UC3Music/uC3Moy/Media/Photo/Photo 2.jpg

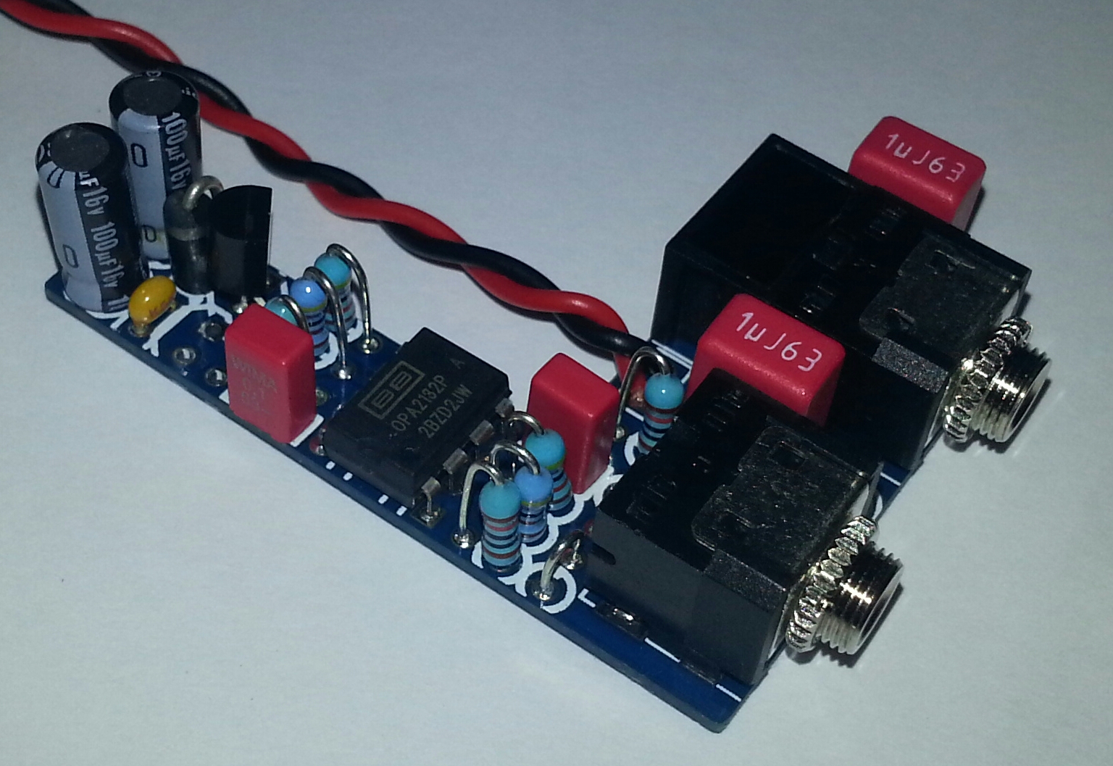
Media/Photo/Photo 2.jpg
