UC3Music/uC3Moy/Media/Photo/Photo 3.jpg

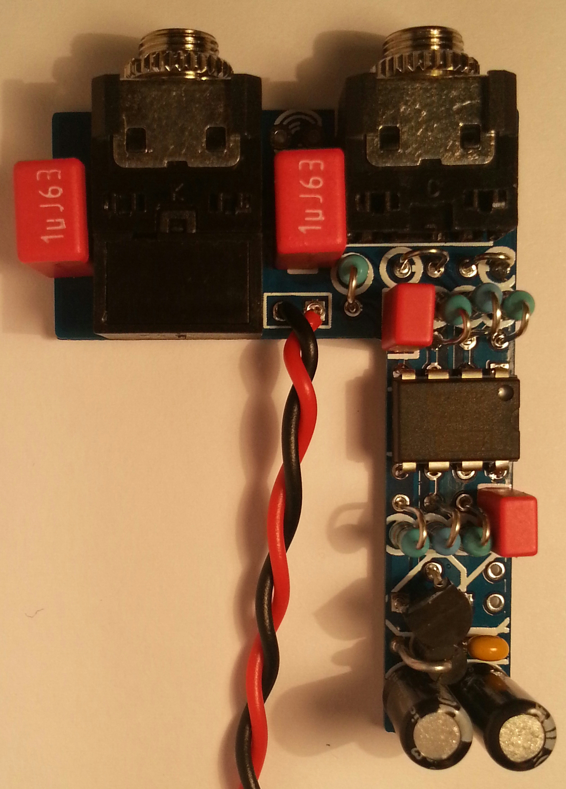
Media/Photo/Photo 3.jpg
