UC3Music/uC3Moy/Media/Photo/Yellow Fashion.jpg

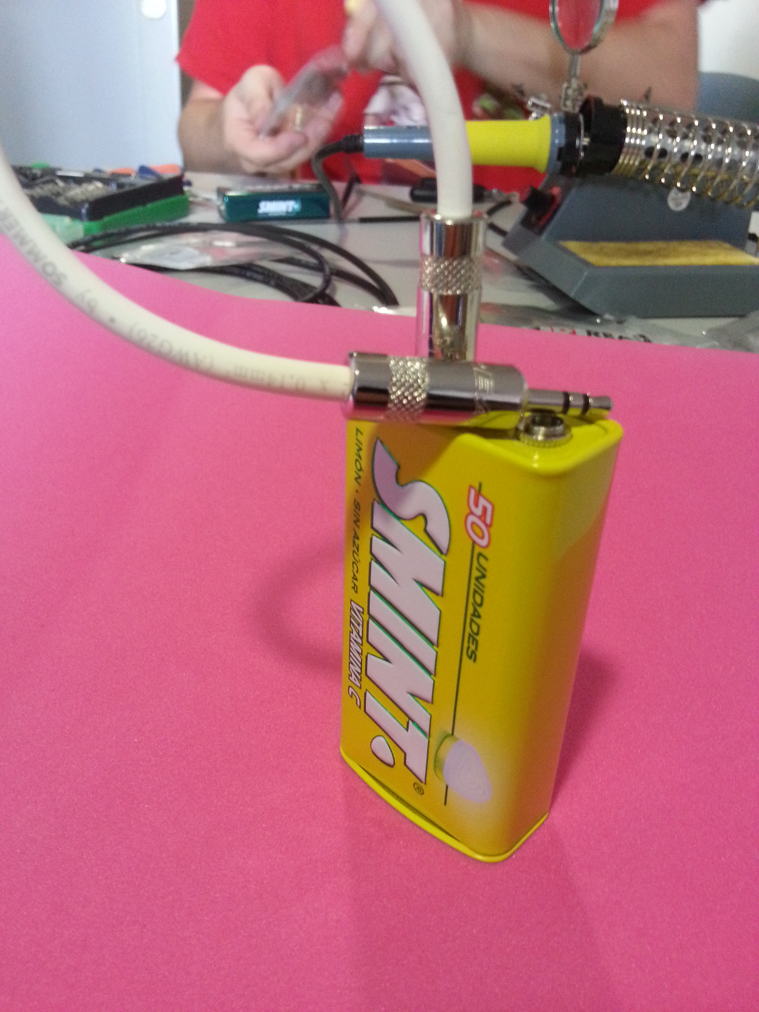
Media/Photo/Yellow Fashion.jpg
