UC3Music/uC3Moy/Media/Simulated Angled View 2.JPG

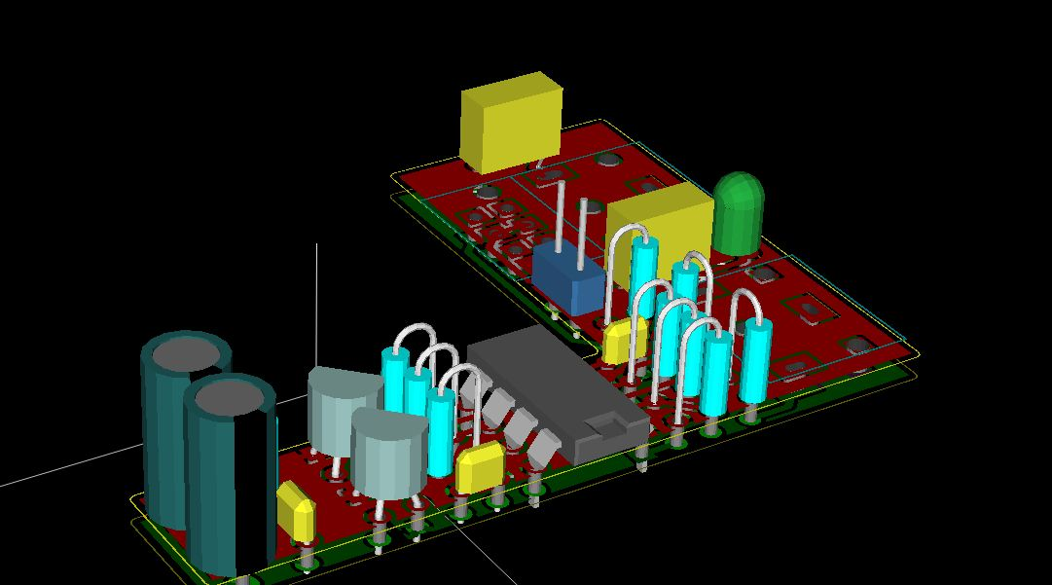
Media/Simulated Angled View 2.JPG
