UC3Music/uC3Moy/Media/Simulated Angled View.JPG

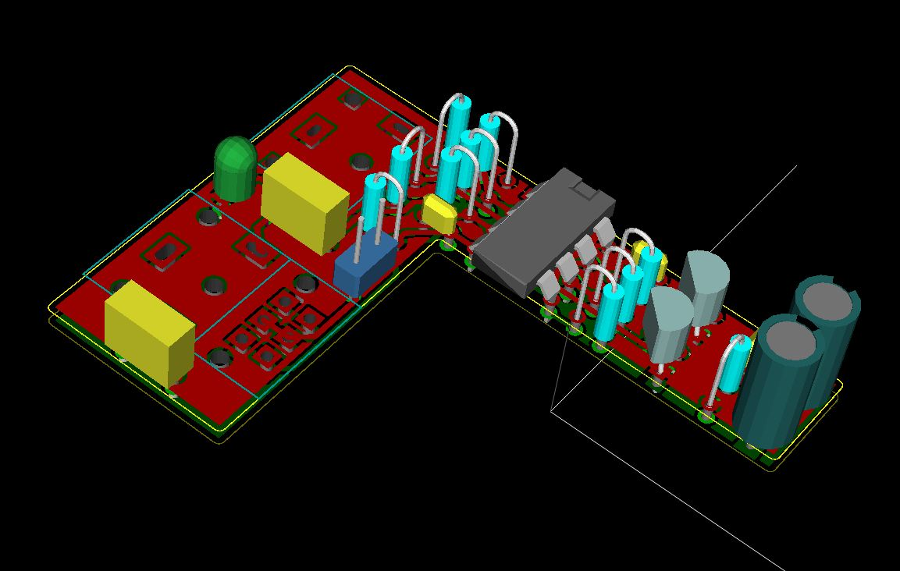
Media/Simulated Angled View.JPG
